OlegDemk/ESP32_GPS_loger_v1/2. Firmware/main/main.h

#ifndef MAIN_H
#define MAIN_H

#include <stdio.h>
#include <stdbool.h>
#include <stddef.h>
#include <stdlib.h>
#include <inttypes.h>
#include "sdkconfig.h"
#include "freertos/FreeRTOS.h"
#include "freertos/task.h"
#include "esp_chip_info.h"
#include "esp_flash.h"
#include "esp_log.h"
#include "string.h"
#include "stdint.h"
#include "esp_system.h"
#include "nvs_flash.h"
#include "nvs.h"
// ------------------------------------------------------------------------------------------------------------------
#include "driver/i2c.h"
#include "bme280/bme280.h"
#include "bme280/main_bme280.h"
// ------------------------------------------------------------------------------------------------------------------
#include "driver/gpio.h"
#include "leds_gpio/leds_gpio.h"
// ------------------------------------------------------------------------------------------------------------------
#include "esp_heap_caps.h"
// ------------------------------------------------------------------------------------------------------------------
#include "nvs_flash.h"
#include "nvs.h"
#include "microsd/mount.h"
// ------------------------------------------------------------------------------------------------------------------
#include "driver/uart.h"
#include "gps/main_gps.h"
#include "gps/nmea_parser.h"
// ------------------------------------------------------------------------------------------------------------------
#include "gsm/gsm_sim800l.h"
// ------------------------------------------------------------------------------------------------------------------
#include "esp_spiffs.h"
#include "spiffs_config.h"
#include "esp_netif.h"
#include "esp_event.h"
#include "wifi/http.h"
#include "wifi/wifi.h"
// ------------------------------------------------------------------------------------------------------------------
#include "driver/adc.h"
#include "esp_adc_cal.h"
#include "buttery/buttery.h"
// ------------------------------------------------------------------------------------------------------------------
#include "gps_data.h"

#define ON 1
#define OFF 0

#define SMS_FITBACK ON

// ------------------------------------------------------------------------------------------
typedef struct {
	float temperature;
	float humidity;
	float preassure;
} bme280_thp_t;
// ------------------------------------------------------------------------------------------
typedef struct{
	uint8_t battery_level;
} battery_t;
// ------------------------------------------------------------------------------------------

void gps_log_on(void);
void gps_log_off(void);
void send_one_point_gps_data(void);
void restart_all_esp32(void);

void task_log_data_into_file(void *ignore);
void send_sms_message_plus_battery_level(char *message);
void stop_http_server(void);

#endif // MAIN_H
